mnezerka/blue-sensors/esp8266/src/SerialWriter.h

#ifndef SERIALWRITER_H
#define SERIALWRITER_H

#include "DeviceStateListener.h"
#include "Sensors.h"

class SerialWriter: public DeviceStateListener
{
    public:

    void begin()
    {
        // initialize serial port
        Serial.begin(9600);
        Serial.println("Serial port initialized");
    }

    void state(String state)
    {
        Serial.println("New state: " + state);
    }

    void debug(String msg)
    {
        Serial.println(msg);
    }

    void processReadings()
    {
        Serial.println("Current readings:");

        // get all sensor readings and generate appropriate HTML representation
        for(int i = 0; i < Sensors::getInstance().getSensors()->size(); i++)
        {
            Sensor *sensor = Sensors::getInstance().getSensors()->get(i);
            Reading* reading = sensor->getReadings();
            while (!reading->isLast)
            {
                Serial.println("  " + reading->address + ": " + String(reading->temperature) + "C");
                reading++;
            }
        }
    }
};

#endif
