mnezerka/blue-sensors/esp8266/src/WifiConnectivity.h

#ifndef WIFICONNECTIVITY_H
#define WIFICONNECTIVITY_H

//#include <Ethernet.h>
#include <WiFiManager.h>
#include "DeviceState.h"

class WifiConnectivity
{
  public:

    void begin()
    {
        DeviceState::getInstance().state("Init wifi manager");
        //wifiManager.resetSettings();  // this can be used to reset rembembered SID
        WiFiManager wifiManager;
        wifiManager.setTimeout(300);
        wifiManager.autoConnect("ESP8266 Settings");
    }
};

#endif
